Ascend-Huawei/Obstacle_Avoidance_Stack/Assets/7.jpg

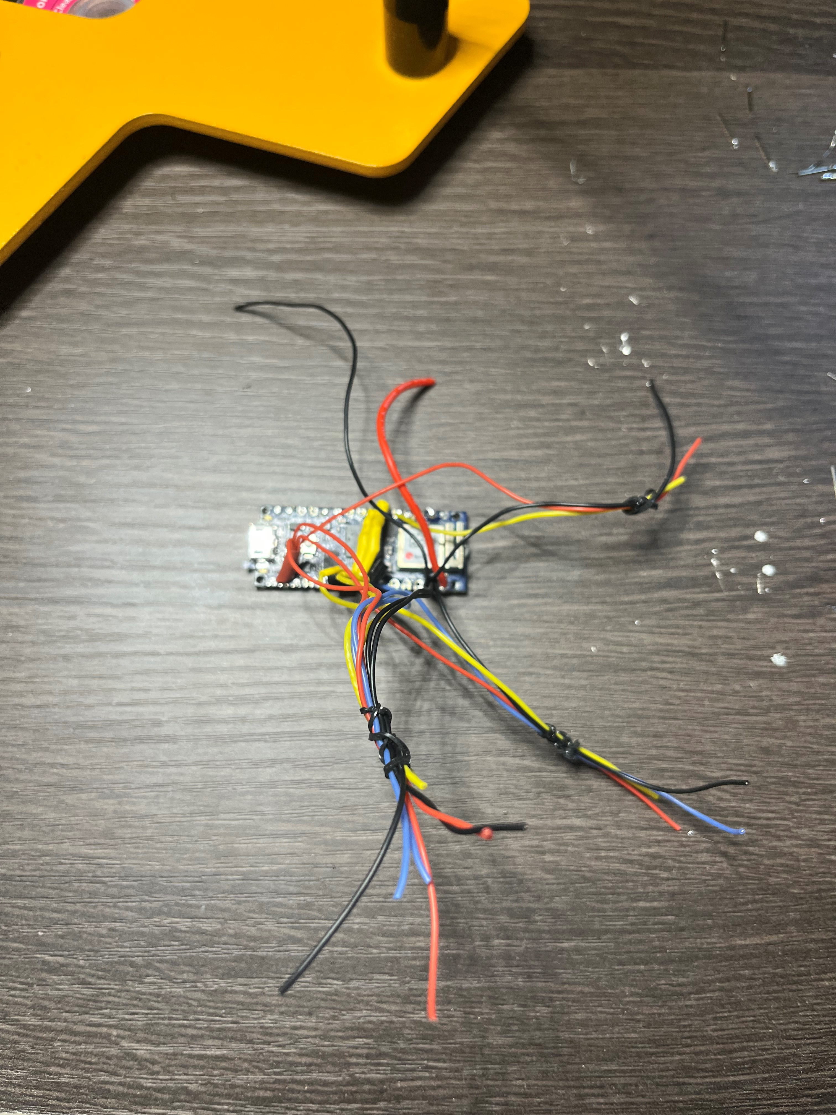
Assets/7.jpg
