Ascend-Huawei/Obstacle_Avoidance_Stack/Assets/12.jpg

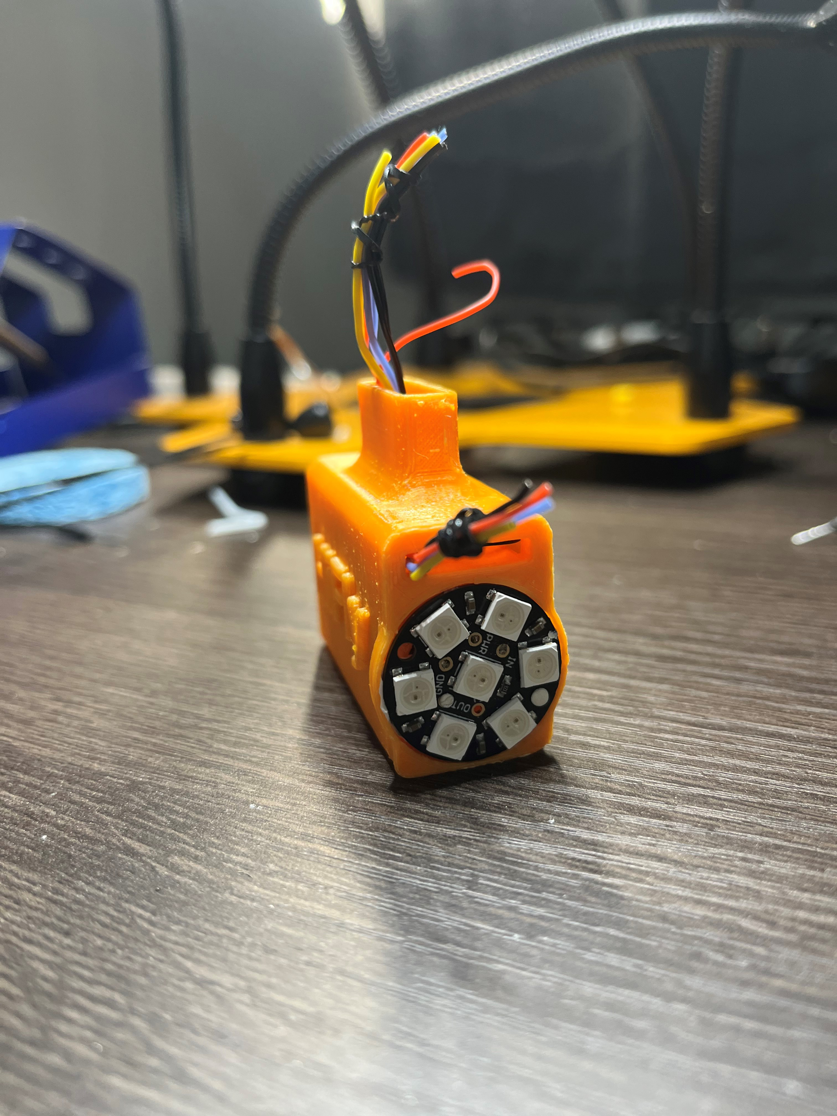
Assets/12.jpg
