Ascend-Huawei/Obstacle_Avoidance_Stack/Assets/14.jpg

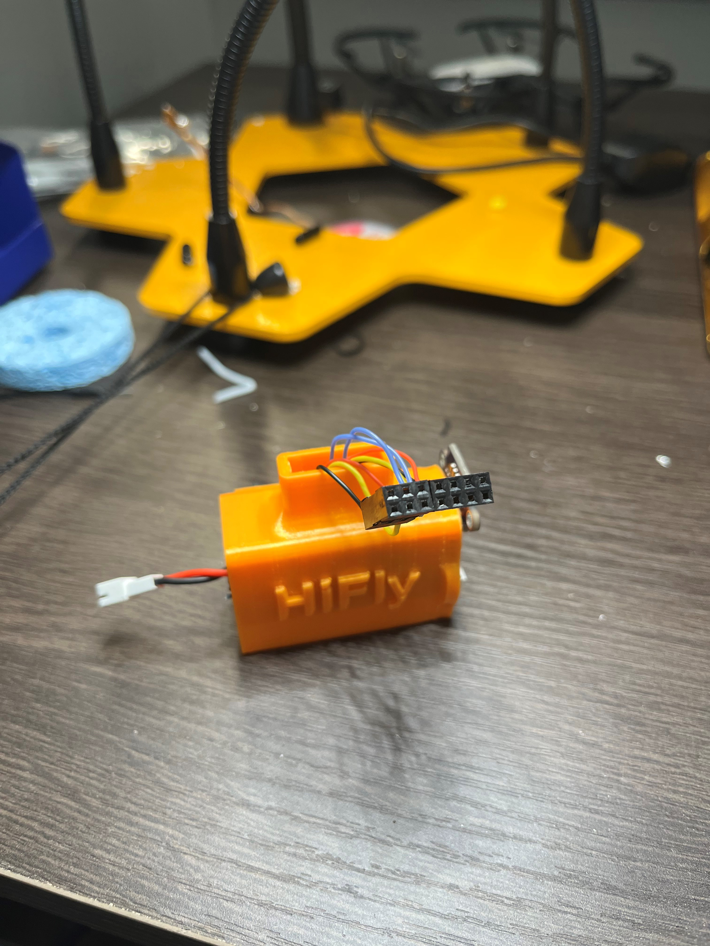
Assets/14.jpg
