Ascend-Huawei/Obstacle_Avoidance_Stack/Assets/hatch3.jpg

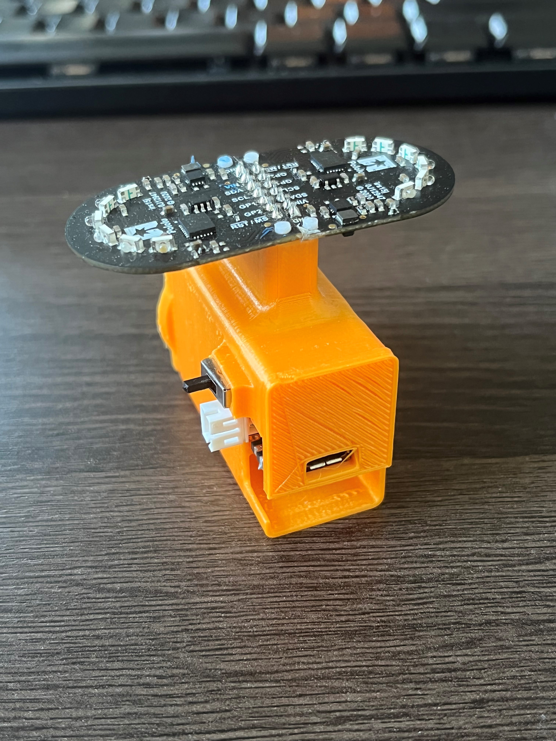
Assets/hatch3.jpg
