Ascend-Huawei/Obstacle_Avoidance_Stack/Assets/module_drone2.jpg

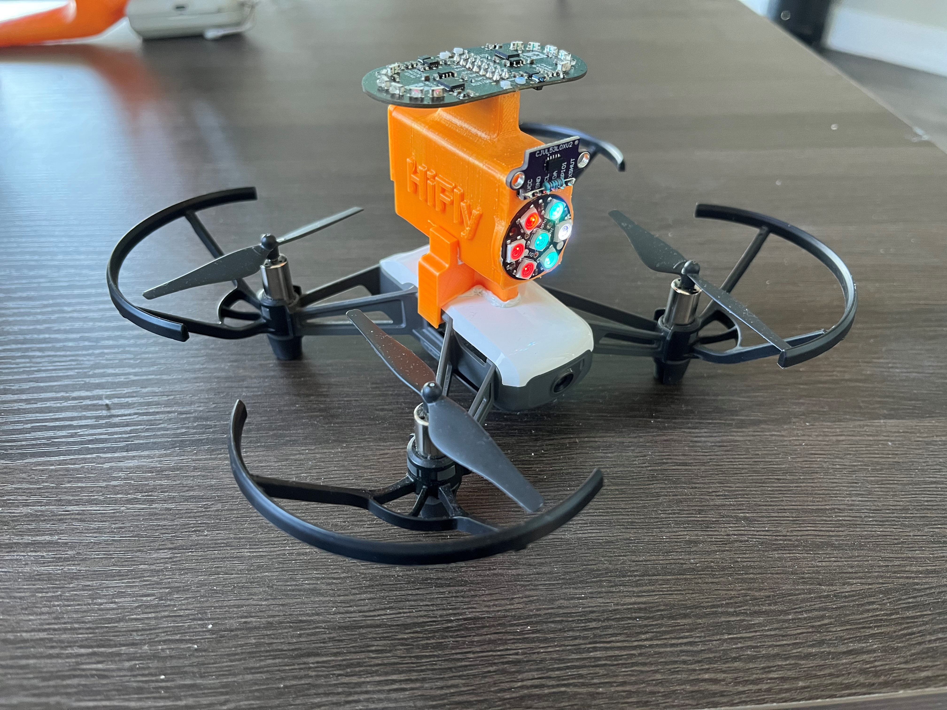
Assets/module_drone2.jpg
