Ascend-Huawei/Obstacle_Avoidance_Stack/Assets/module_only.jpg

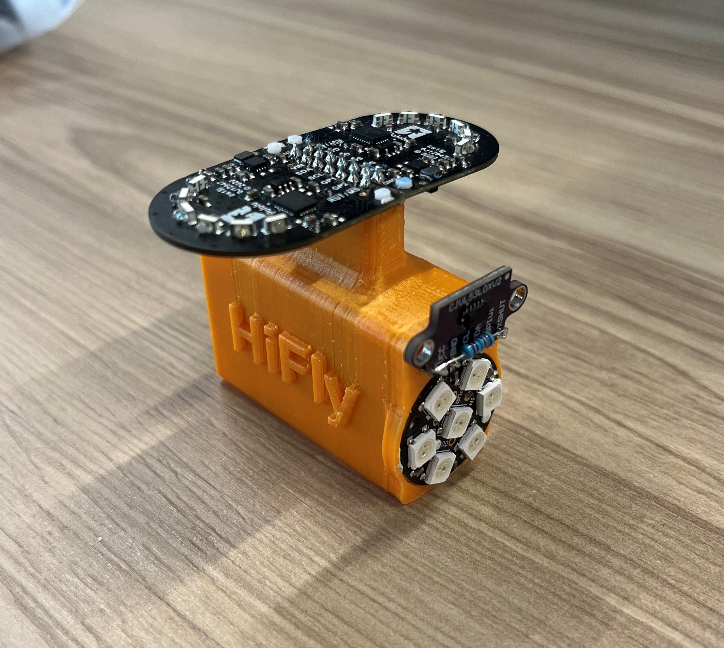
Assets/module_only.jpg
