Ascend-Huawei/Obstacle_Avoidance_Stack/Atlas200DK/Assets/tplink_1.JPG

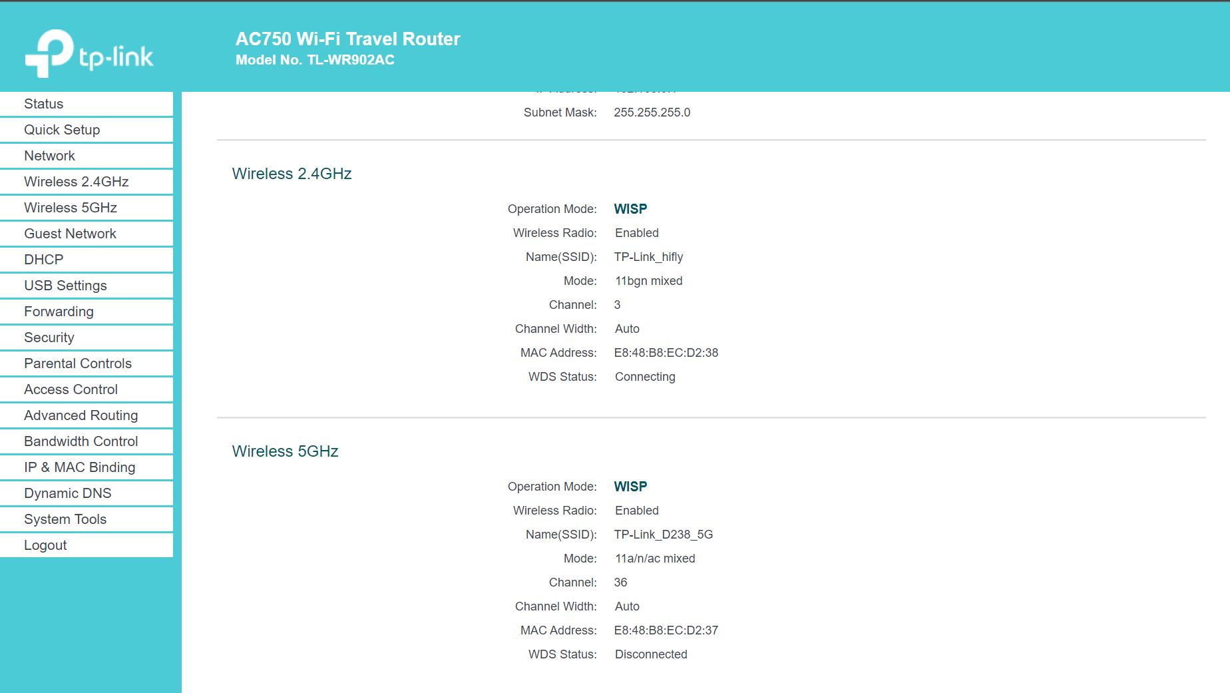
Atlas200DK/Assets/tplink_1.JPG
