Ascend-Huawei/Obstacle_Avoidance_Stack/Assets/2.jpg

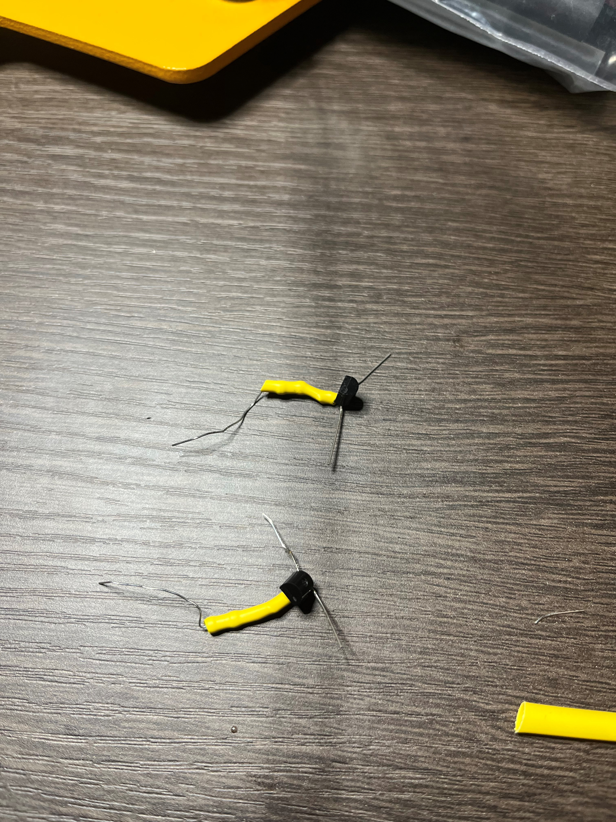
Assets/2.jpg
