Ascend-Huawei/Obstacle_Avoidance_Stack/Assets/3.jpg

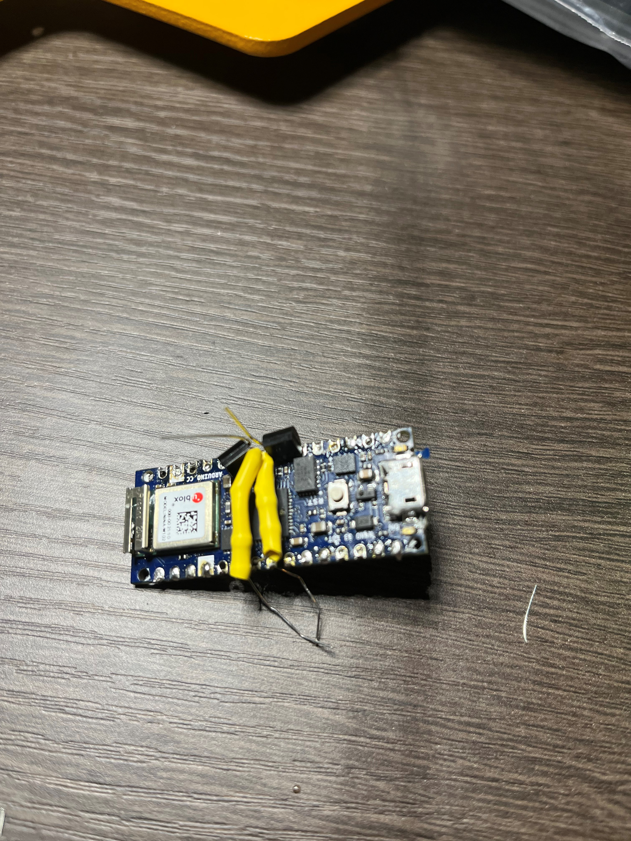
Assets/3.jpg
