Ascend-Huawei/Obstacle_Avoidance_Stack/Assets/4.jpg

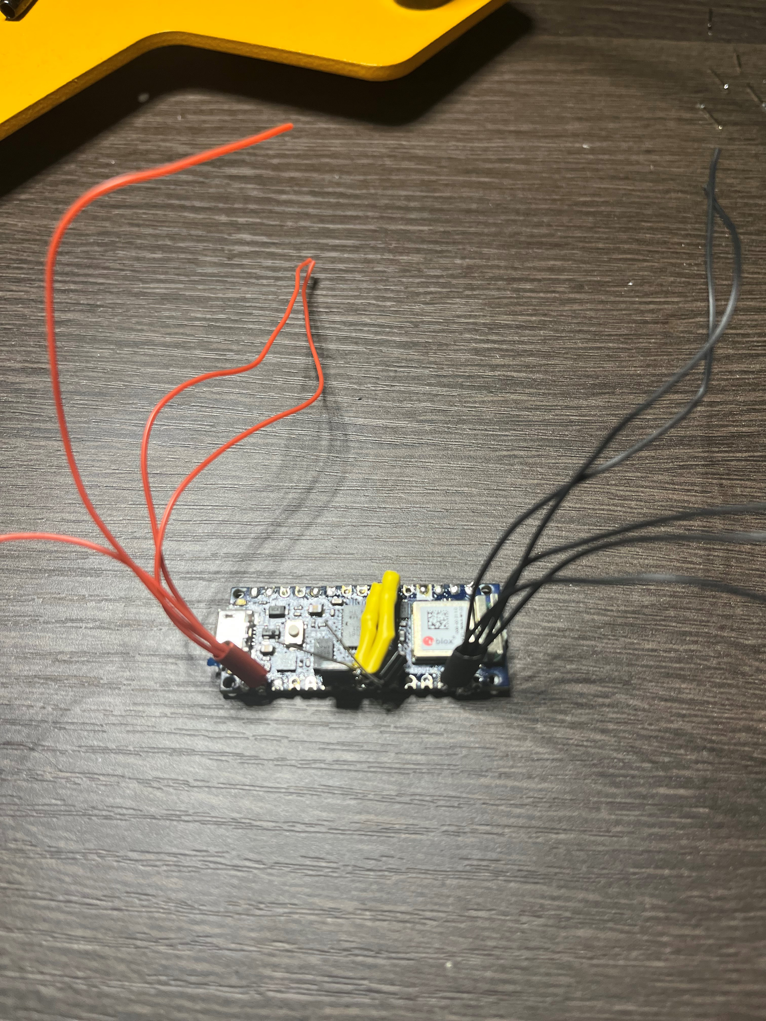
Assets/4.jpg
