Ascend-Huawei/Obstacle_Avoidance_Stack/Assets/5.jpg

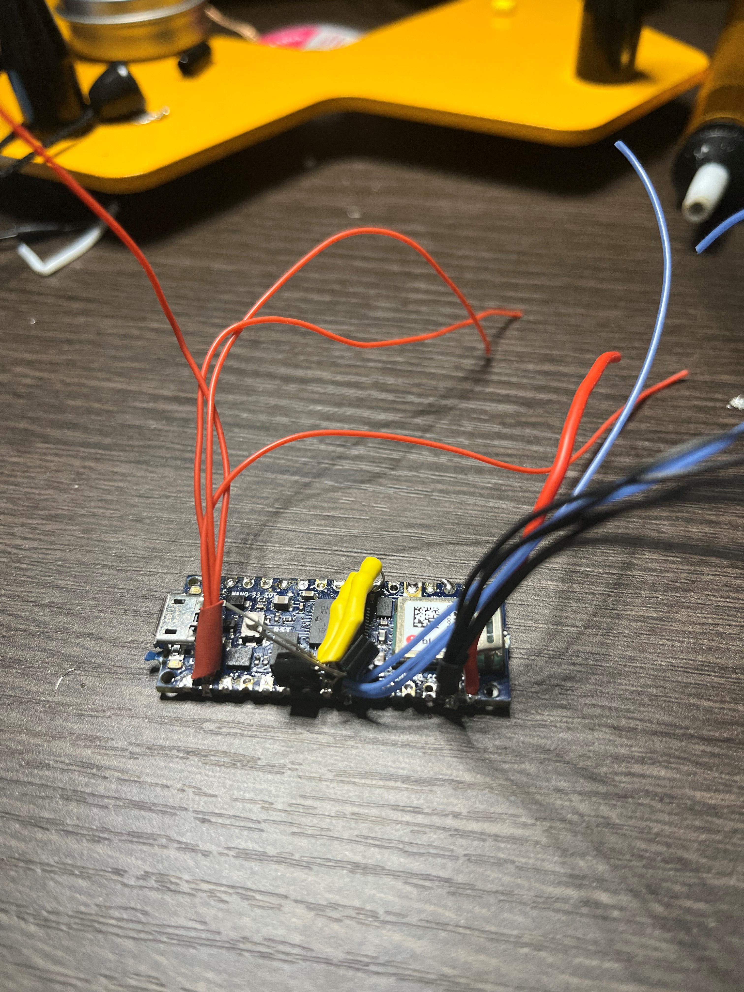
Assets/5.jpg
