Ascend-Huawei/Obstacle_Avoidance_Stack/Assets/6.jpg

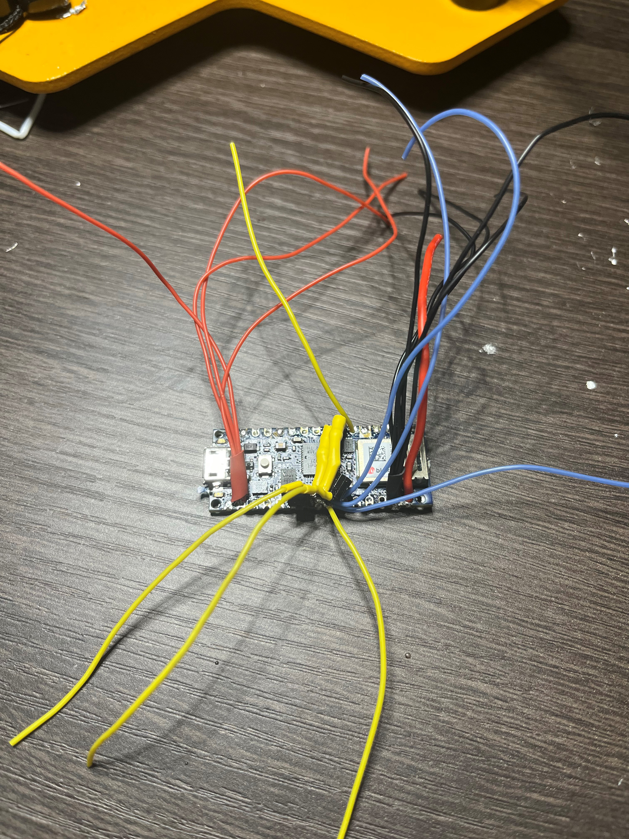
Assets/6.jpg
