Ascend-Huawei/Obstacle_Avoidance_Stack/Assets/8.jpg

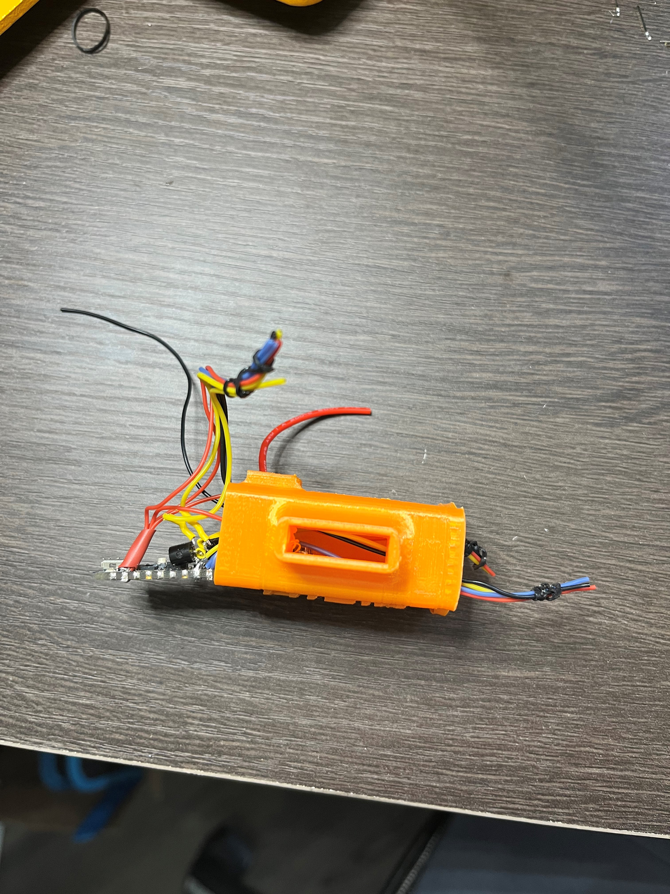
Assets/8.jpg
