Ascend-Huawei/Obstacle_Avoidance_Stack/Assets/9.jpg

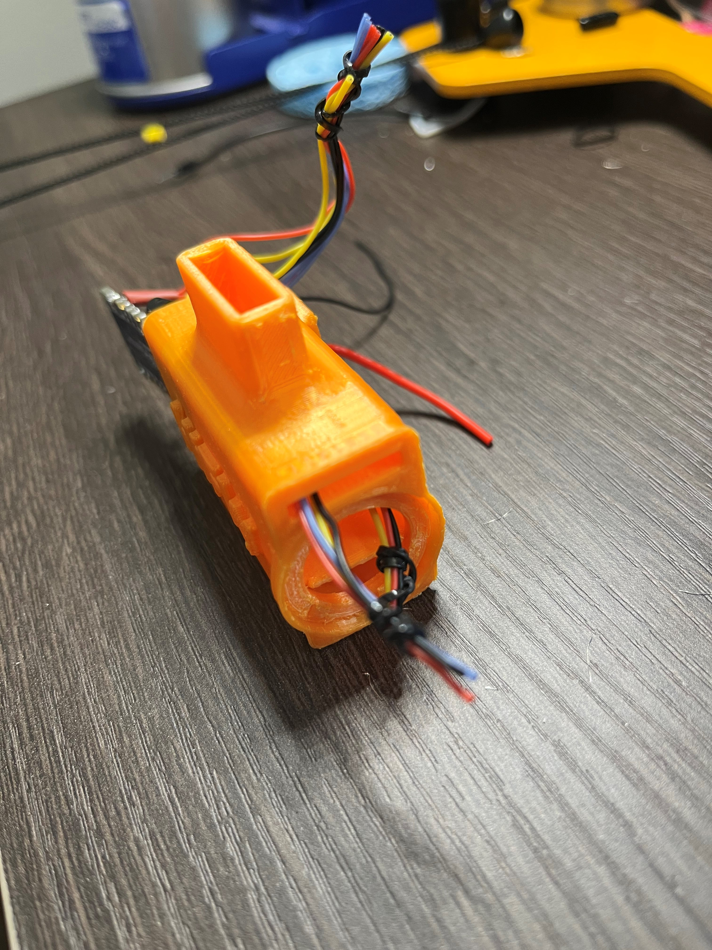
Assets/9.jpg
