Ascend-Huawei/Obstacle_Avoidance_Stack/Assets/10.jpg

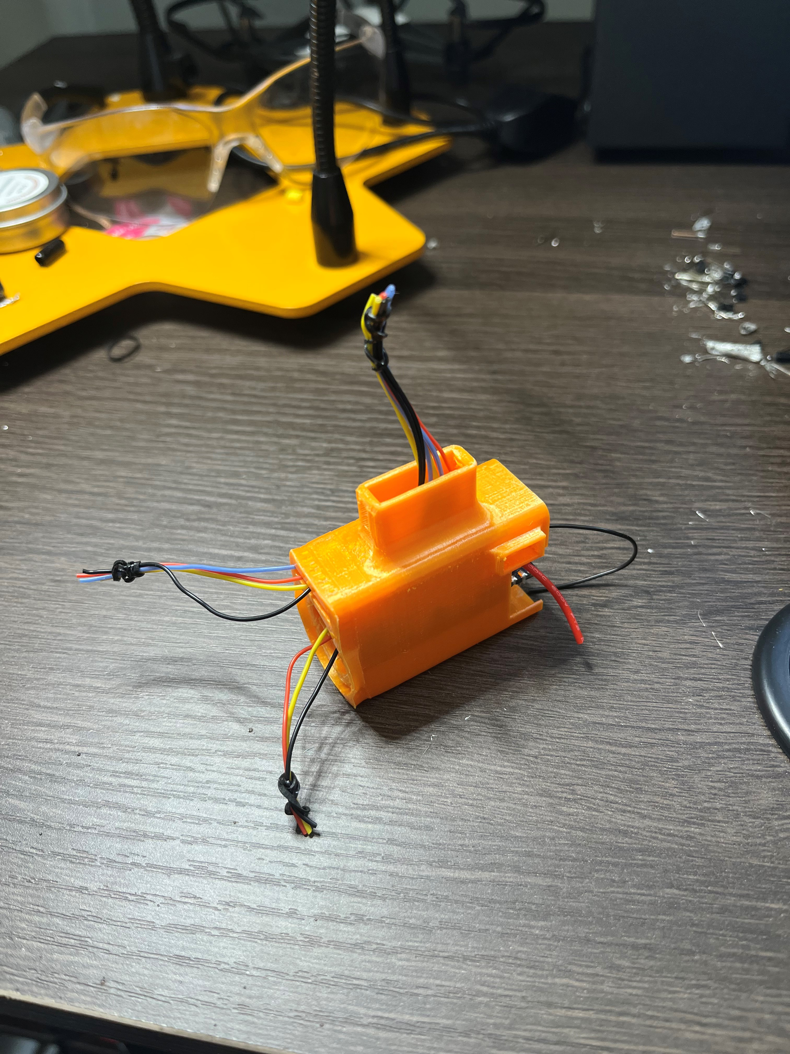
Assets/10.jpg
