Ascend-Huawei/Obstacle_Avoidance_Stack/Assets/11.jpg

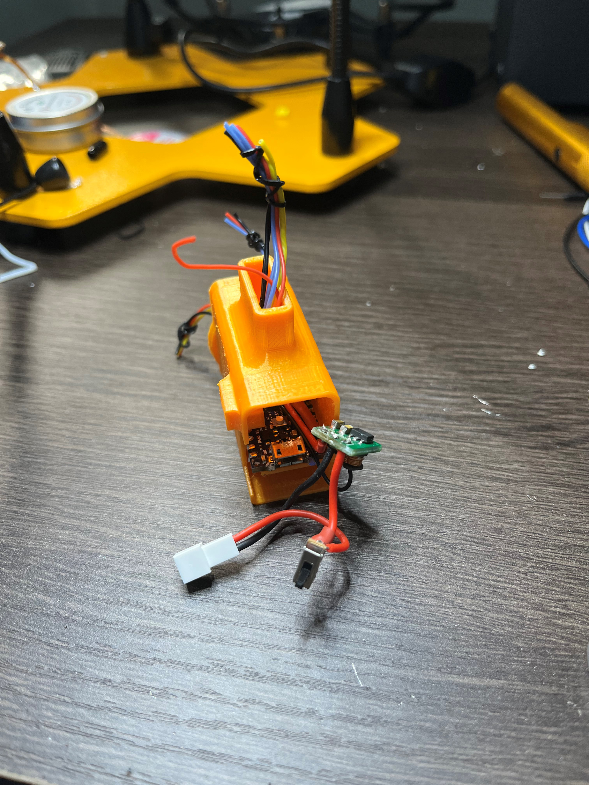
Assets/11.jpg
