Ascend-Huawei/Obstacle_Avoidance_Stack/Assets/13.jpg

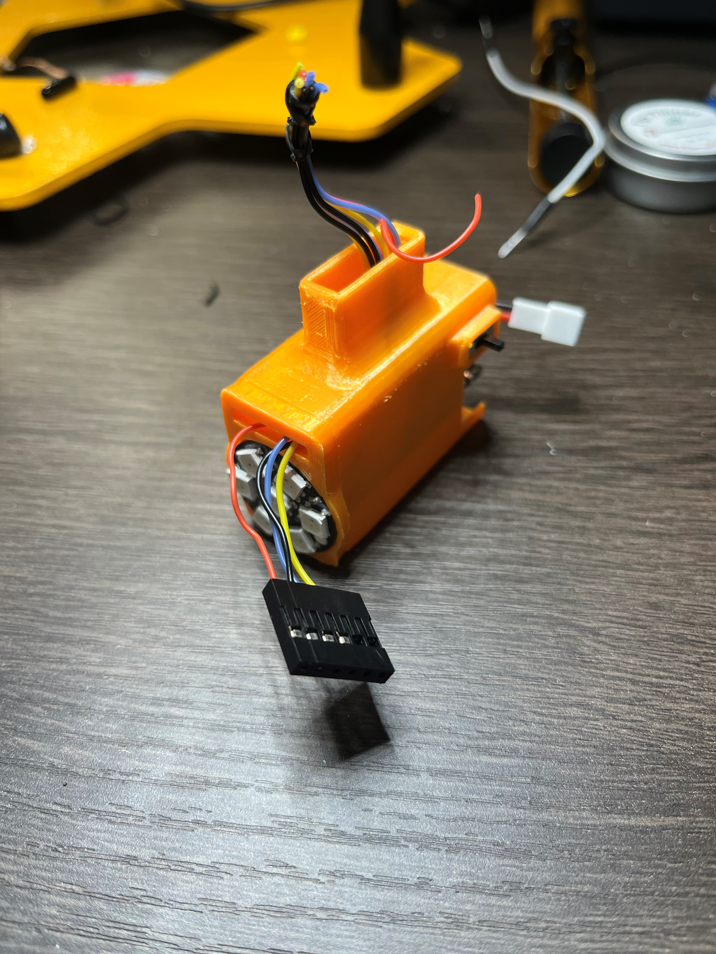
Assets/13.jpg
