Ascend-Huawei/Obstacle_Avoidance_Stack/Assets/15.jpg

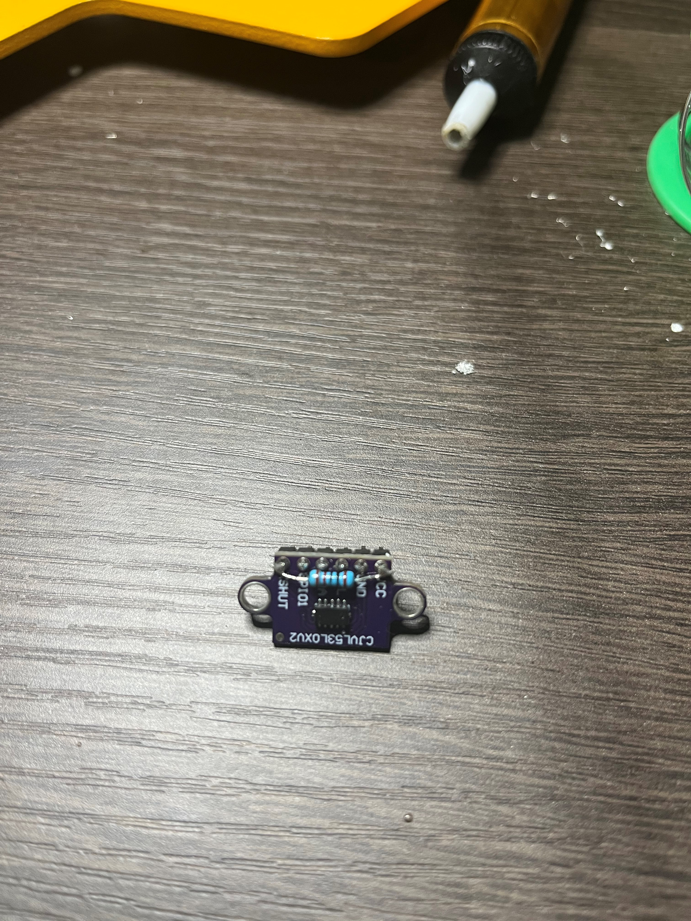
Assets/15.jpg
